hgrf/el-poisson-billy/hw/el_poisson_billy_rev1.kicad_sch

## KiCad design hw/el_poisson_billy_rev1.kicad_sch (2023-11-04)

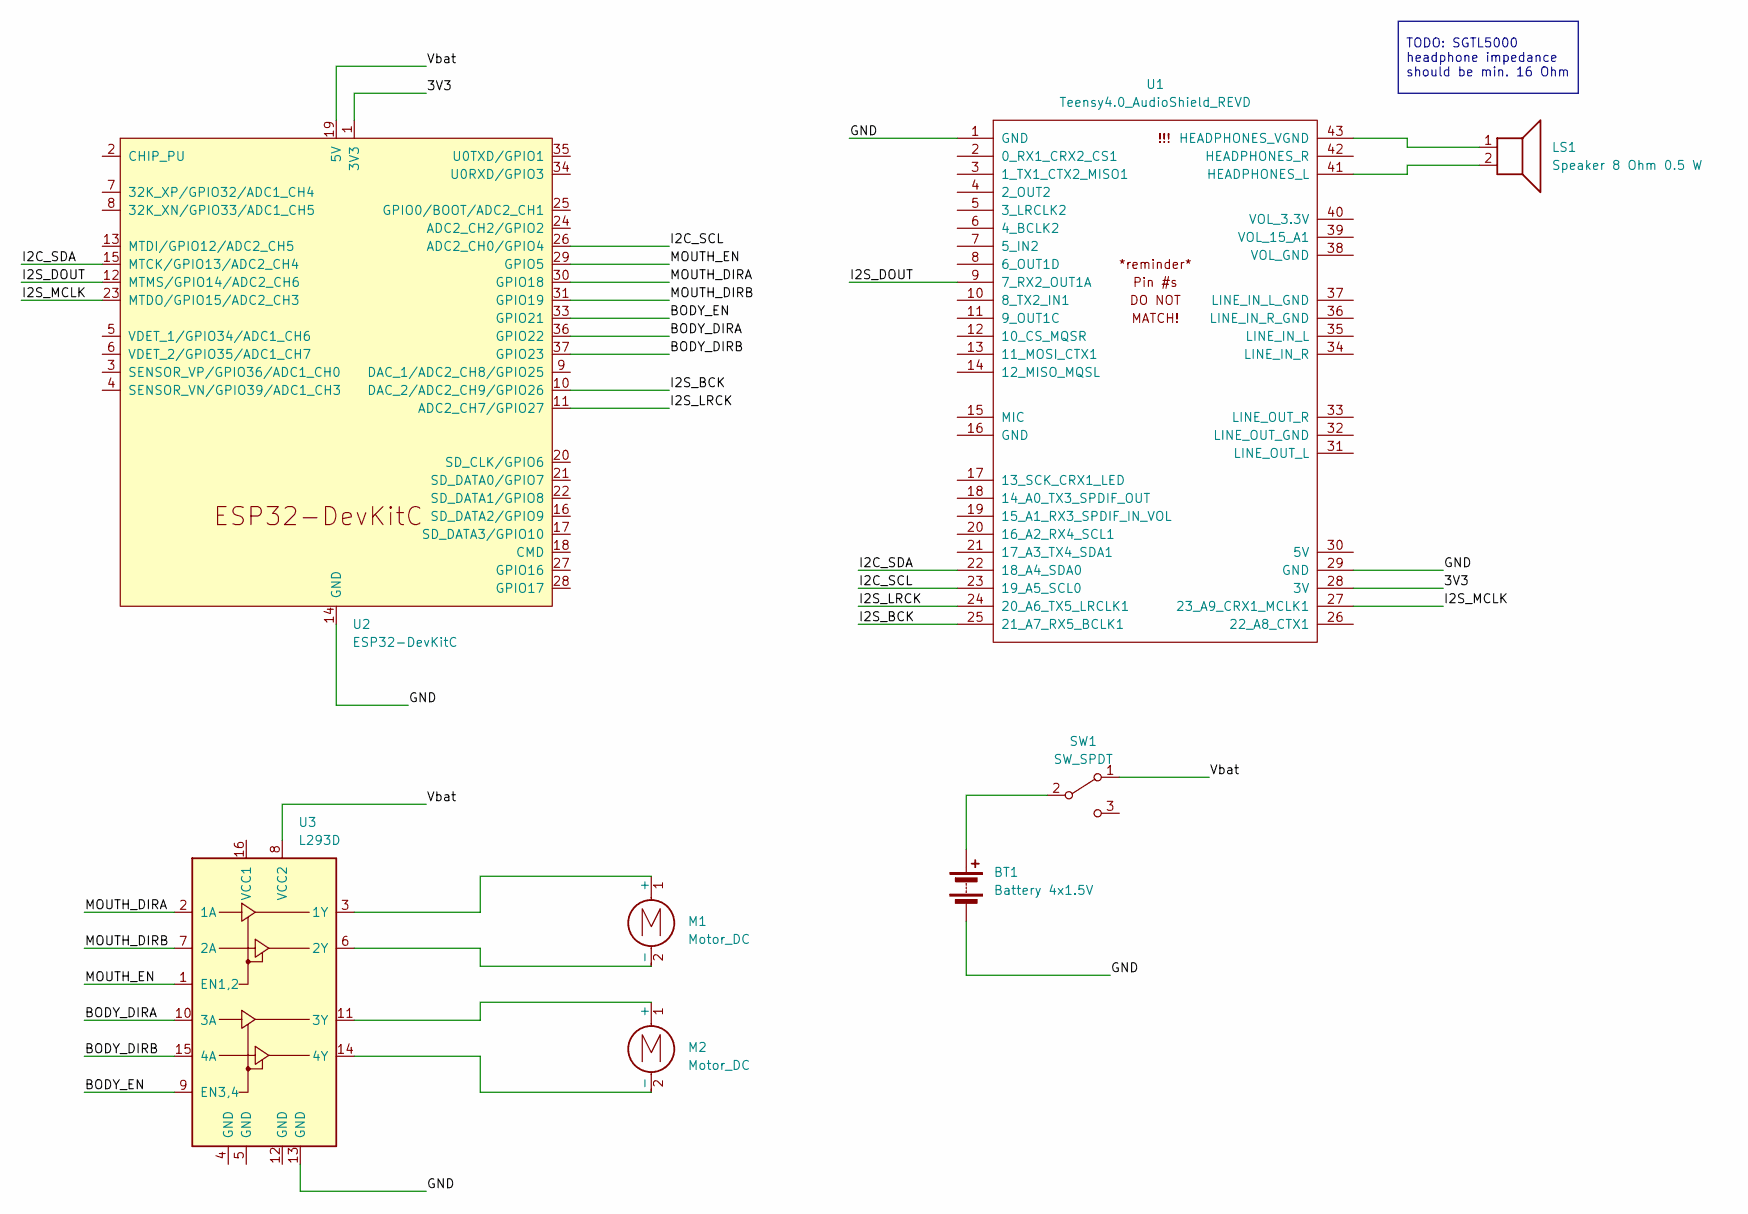
[picture p4: schematic el_poisson_billy_rev1.kicad_sch]

Parts:
BT1: Battery 4x1.5V
LS1: Speaker 8 Ohm 0.5 W
M1, M2: Motor_DC
SW1: SW_SPDT
U1: Teensy4.0_AudioShield_REVD; 4.0audioshield
U2: ESP32-DevKitC
U3: L293D; DIP-16_W7.62mm

Connections:
3V3: U1.28 (3V), U2.1 (3V3)
BODY_DIRA: U2.36 (GPIO22), U3.10 (3A)
BODY_DIRB: U2.37 (GPIO23), U3.15 (4A)
BODY_EN: U2.33 (GPIO21), U3.9 (EN3,4)
GND: BT1.2 (-), U1.1 (GND), U1.29 (GND), U2.14 (GND), U2.32 (GND), U2.38 (GND), U3.13 (GND)
I2C_SCL: U1.23 (19_A5_SCL0), U2.26 (ADC2_CH0/GPIO4)
I2C_SDA: U1.22 (18_A4_SDA0), U2.15 (MTCK/GPIO13/ADC2_CH4)
I2S_BCK: U1.25 (21_A7_RX5_BCLK1), U2.10 (DAC_2/ADC2_CH9/GPIO26)
I2S_DOUT: U1.9 (7_RX2_OUT1A), U2.12 (MTMS/GPIO14/ADC2_CH6)
I2S_LRCK: U1.24 (20_A6_TX5_LRCLK1), U2.11 (ADC2_CH7/GPIO27)
I2S_MCLK: U1.27 (23_A9_CRX1_MCLK1), U2.23 (MTDO/GPIO15/ADC2_CH3)
MOUTH_DIRA: U2.30 (GPIO18), U3.2 (1A)
MOUTH_DIRB: U2.31 (GPIO19), U3.7 (2A)
MOUTH_EN: U2.29 (GPIO5), U3.1 (EN1,2)
unnamed: BT1.1 (+), SW1.2 (B)
unnamed: LS1.1, U1.43 (HEADPHONES_VGND)
unnamed: LS1.2, U1.41 (HEADPHONES_L)
unnamed: M1.1 (+), U3.3 (1Y)
unnamed: M1.2 (-), U3.6 (2Y)
unnamed: M2.1 (+), U3.11 (3Y)
unnamed: M2.2 (-), U3.14 (4Y)
Vbat: SW1.1 (A), U2.19 (5V), U3.8 (VCC2)

Notes on the sheet:
TODO: SGTL5000 headphone impedance should be min. 16 Ohm
