hgrf/el-poisson-billy/main/bt_app_spp.c

#include "bt_app_spp.h"

#include <inttypes.h>

#include "esp_log.h"

#include "body.h"

#define SPP_TAG "SPP"
#define SPP_SERVER_NAME "SPP_SERVER"

static const esp_spp_sec_t sec_mask = ESP_SPP_SEC_AUTHENTICATE;
static const esp_spp_role_t role_slave = ESP_SPP_ROLE_SLAVE;

static char *bda2str(uint8_t * bda, char *str, size_t size)
{
    if (bda == NULL || str == NULL || size < 18) {
        return NULL;
    }

    uint8_t *p = bda;
    sprintf(str, "%02x:%02x:%02x:%02x:%02x:%02x",
            p[0], p[1], p[2], p[3], p[4], p[5]);
    return str;
}

void esp_spp_cb(esp_spp_cb_event_t event, esp_spp_cb_param_t *param)
{
    char bda_str[18] = {0};

    switch (event) {
    case ESP_SPP_INIT_EVT:
        if (param->init.status == ESP_SPP_SUCCESS) {
            ESP_LOGI(SPP_TAG, "ESP_SPP_INIT_EVT");
            esp_spp_start_srv(sec_mask, role_slave, 0, SPP_SERVER_NAME);
        } else {
            ESP_LOGE(SPP_TAG, "ESP_SPP_INIT_EVT status:%d", param->init.status);
        }
        break;
    case ESP_SPP_DISCOVERY_COMP_EVT:
        ESP_LOGI(SPP_TAG, "ESP_SPP_DISCOVERY_COMP_EVT");
        break;
    case ESP_SPP_OPEN_EVT:
        ESP_LOGI(SPP_TAG, "ESP_SPP_OPEN_EVT");
        break;
    case ESP_SPP_CLOSE_EVT:
        ESP_LOGI(SPP_TAG, "ESP_SPP_CLOSE_EVT status:%d handle:%"PRIu32" close_by_remote:%d", param->close.status,
                 param->close.handle, param->close.async);
        break;
    case ESP_SPP_START_EVT:
        if (param->start.status == ESP_SPP_SUCCESS) {
            ESP_LOGI(SPP_TAG, "ESP_SPP_START_EVT handle:%"PRIu32" sec_id:%d scn:%d", param->start.handle, param->start.sec_id,
                     param->start.scn);
        } else {
            ESP_LOGE(SPP_TAG, "ESP_SPP_START_EVT status:%d", param->start.status);
        }
        break;
    case ESP_SPP_CL_INIT_EVT:
        ESP_LOGI(SPP_TAG, "ESP_SPP_CL_INIT_EVT");
        break;
    case ESP_SPP_DATA_IND_EVT:
        /*
         * We only show the data in which the data length is less than 128 here. If you want to print the data and
         * the data rate is high, it is strongly recommended to process them in other lower priority application task
         * rather than in this callback directly. Since the printing takes too much time, it may stuck the Bluetooth
         * stack and also have a effect on the throughput!
         */
        ESP_LOGI(SPP_TAG, "ESP_SPP_DATA_IND_EVT len:%"PRIu16" handle:%"PRIu32,
                 param->data_ind.len, param->data_ind.handle);
        if (param->data_ind.len < 128) {
            esp_log_buffer_hex("", param->data_ind.data, param->data_ind.len);
        }

        switch(param->data_ind.data[0]) {
        case 'o':
            body_open_mouth();
            break;
        case 'c':
            body_close_mouth();
            break;
        case 'h':
            body_wiggle_head();
            break;
        case 't':
            body_wiggle_tail();
            break;
        case 's':
            body_wiggle_stop();
            break;
        }
        break;
    case ESP_SPP_CONG_EVT:
        ESP_LOGI(SPP_TAG, "ESP_SPP_CONG_EVT");
        break;
    case ESP_SPP_WRITE_EVT:
        ESP_LOGI(SPP_TAG, "ESP_SPP_WRITE_EVT");
        break;
    case ESP_SPP_SRV_OPEN_EVT:
        ESP_LOGI(SPP_TAG, "ESP_SPP_SRV_OPEN_EVT status:%d handle:%"PRIu32", rem_bda:[%s]", param->srv_open.status,
                 param->srv_open.handle, bda2str(param->srv_open.rem_bda, bda_str, sizeof(bda_str)));
        break;
    case ESP_SPP_SRV_STOP_EVT:
        ESP_LOGI(SPP_TAG, "ESP_SPP_SRV_STOP_EVT");
        break;
    case ESP_SPP_UNINIT_EVT:
        ESP_LOGI(SPP_TAG, "ESP_SPP_UNINIT_EVT");
        break;
    default:
        break;
    }
}
